sbstnh/programmable_precision_resistor/firmware/main/Core/Inc/build_def.h

/**
 * @file    build_def.h
 * @author  sebas
 * @date    08.01.2023
 * @brief	Build defintion
 */
#ifndef INC_BUILD_DEF_H_
#define INC_BUILD_DEF_H_

/* Includes ------------------------------------------------------------------*/
/* Exported constants --------------------------------------------------------*/

#define VERSION_STRING_UI_MAX_LEN		32

/* Exported types ------------------------------------------------------------*/
/* Exported macro ------------------------------------------------------------*/
/* Exported variables --------------------------------------------------------*/

extern const char VERSION_STRING_MAINBOARD[];
extern char VERSION_STRING_UI[VERSION_STRING_UI_MAX_LEN];

/* Private constants ---------------------------------------------------------*/
/* Private macros ------------------------------------------------------------*/
/* Exported functions --------------------------------------------------------*/
/* Private functions ---------------------------------------------------------*/

#endif /* INC_BUILD_DEF_H_ */
