sbstnh/programmable_precision_resistor/firmware/main/Core/Inc/hardware/eeprom_def.h

/**
 * @file    eeprom_def.h
 * @author  sebas
 * @date    20.10.2022
 * @brief
 */


#ifndef INC_HARDWARE_EEPROM_DEF_H_
#define INC_HARDWARE_EEPROM_DEF_H_

#include "hardware/eeprom.h"

extern EEPR_TypeDef EEPROM;

#define EEPR_DEVICE_ADDRESS		0b10100000


#endif /* INC_HARDWARE_EEPROM_DEF_H_ */
