sbstnh/programmable_precision_resistor/firmware/main/Core/Inc/hardware/output_def.h

/*
 * output_def.h
 *
 *  Created on: Aug 22, 2021
 *      Author: sebas
 */

#ifndef INC_HARDWARE_OUTPUT_DEF_H_
#define INC_HARDWARE_OUTPUT_DEF_H_

#include "hardware/input_output.h"

/* Digital general purpose outputs for the relay control ----------------------*/

extern const IO_TypeDef OUT_RLY_PWR;
extern const IO_TypeDef OUT_RLY_OE;
extern const IO_TypeDef OUT_RLY_LE;



#endif /* INC_HARDWARE_OUTPUT_DEF_H_ */
