sbstnh/programmable_precision_resistor/firmware/main/Core/Inc/hardware/stp16cp05_def.h

/*
 * stp16cp05_def.h
 *
 *  Created on: 13.10.2022
 *      Author: sebas
 */

#ifndef INC_HARDWARE_STP16CP05_DEF_H_
#define INC_HARDWARE_STP16CP05_DEF_H_

#include "hardware/stp16cp05.h"

extern STP_TypeDef STP;

#endif /* INC_HARDWARE_STP16CP05_DEF_H_ */
