sbstnh/programmable_precision_resistor/firmware/main/Core/Inc/scpi_user_config.h

/*
 * scpi_user_config.h
 *
 *  Created on: 11.11.2022
 *      Author: sebas
 */

#ifndef INC_SCPI_SCPI_USER_CONFIG_H_
#define INC_SCPI_SCPI_USER_CONFIG_H_

#define SCPI_LINE_ENDING		LINE_ENDING_LF

#define USE_FULL_ERROR_LIST		1

#define USE_UNITS_TEMPERATURE	1

#endif /* INC_SCPI_SCPI_USER_CONFIG_H_ */
