sbstnh/programmable_precision_resistor/firmware/main/Core/Inc/version_num.h

/**
 * @file    version_num.h
 * @author  sebas
 * @date    08.01.2023
 * @brief
 */
#ifndef INC_VERSION_NUM_H_
#define INC_VERSION_NUM_H_

/* Includes ------------------------------------------------------------------*/
/* Exported constants --------------------------------------------------------*/

#define VERSION_MAJOR		0
#define VERSION_MINOR		1

/* Exported types ------------------------------------------------------------*/
/* Exported macro ------------------------------------------------------------*/
/* Exported variables --------------------------------------------------------*/
/* Private constants ---------------------------------------------------------*/
/* Private macros ------------------------------------------------------------*/
/* Exported functions --------------------------------------------------------*/
/* Private functions ---------------------------------------------------------*/


#endif /* INC_VERSION_NUM_H_ */
