sbstnh/programmable_precision_resistor/firmware/main/Core/Src/build_def.c

/**
 * @file    build_def.c
 * @author  sebas
 * @date    08.01.2023
 * @brief	Build definition
 *
 */


/* Private typedef -----------------------------------------------------------*/
/* Private macros ------------------------------------------------------------*/
/* Private variables ---------------------------------------------------------*/
/* External variables --------------------------------------------------------*/
/* Exported variables --------------------------------------------------------*/
/* Private function prototypes -----------------------------------------------*/
/* Exported functions --------------------------------------------------------*/

const char VERSION_STRING_MAINBOARD[] = "M2023.09.19T17:28:20";
char VERSION_STRING_UI[] = "";


/* Private functions ---------------------------------------------------------*/
