sbstnh/programmable_precision_resistor/firmware/main/Core/Inc/hardware/ui_interface_def.h

/*
 * ui_interface_def.h
 *
 *  Created on: Nov 6, 2022
 *      Author: sebas
 */

#ifndef INC_HARDWARE_UI_INTERFACE_DEF_H_
#define INC_HARDWARE_UI_INTERFACE_DEF_H_

#include "hardware/ui_interface.h"

#define UIIF_DEVICE_ADDRESS	(0x03 << 1)

extern UIIF_TypeDef UIIF;

#endif /* INC_HARDWARE_UI_INTERFACE_DEF_H_ */
